flyinggorilla/whisper-foiling-catamaran/3dprinting/line-holder-2.jpg

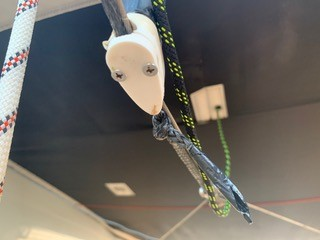
3dprinting/line-holder-2.jpg
