flyinggorilla/whisper-foiling-catamaran/3dprinting/original ride height adjustment wheel.jpg

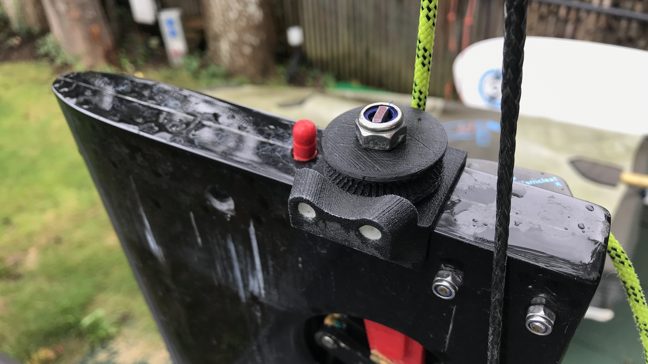
3dprinting/original ride height adjustment wheel.jpg
