flyinggorilla/whisper-foiling-catamaran/3dprinting/ride height knob small.jpg

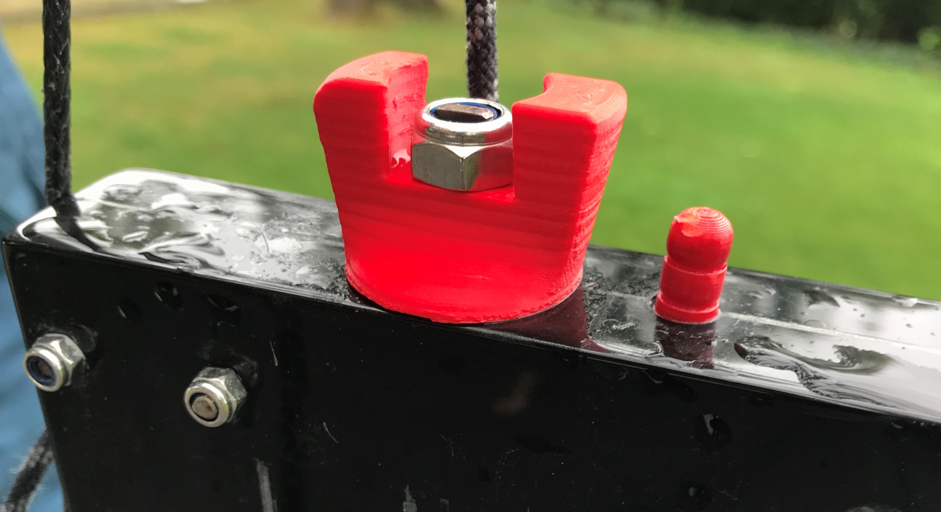
3dprinting/ride height knob small.jpg
