flyinggorilla/whisper-foiling-catamaran/3dprinting/ride height knob.jpg

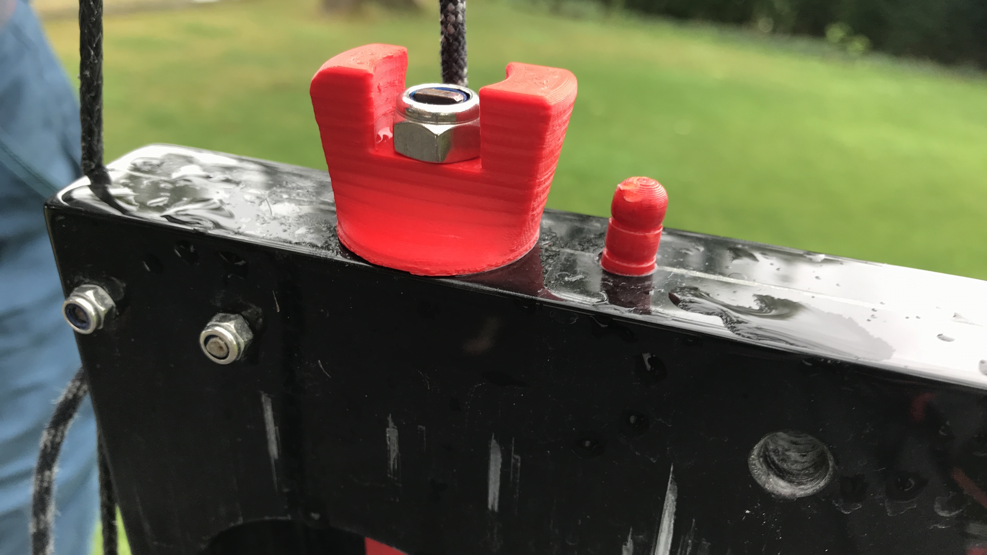
3dprinting/ride height knob.jpg
