flyinggorilla/whisper-foiling-catamaran/3dprinting/ride height knob.png

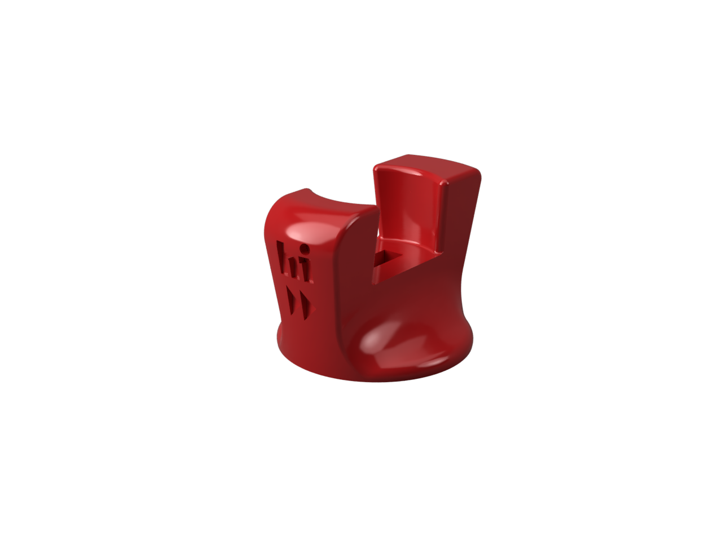
3dprinting/ride height knob.png
