flyinggorilla/whisper-foiling-catamaran/3dprinting/ride height system closeup 1.jpg

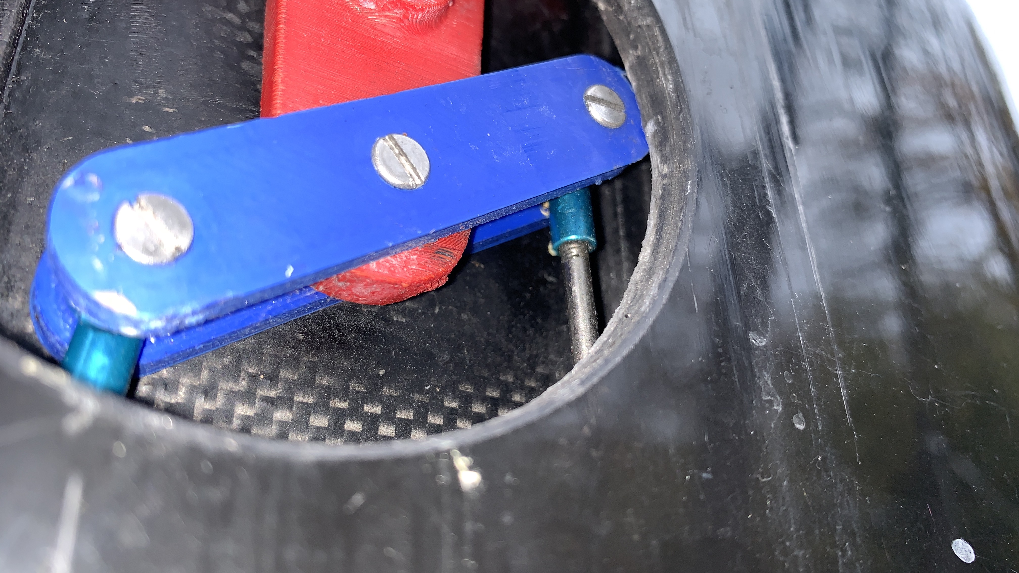
3dprinting/ride height system closeup 1.jpg
