flyinggorilla/whisper-foiling-catamaran/3dprinting/ride height system closeup 3.jpg

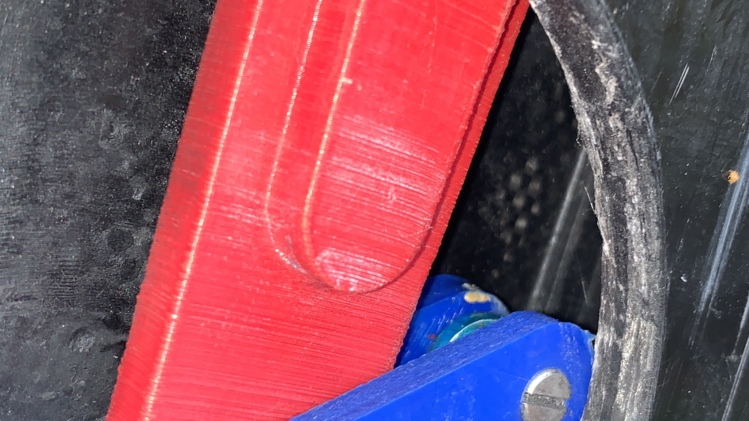
3dprinting/ride height system closeup 3.jpg
