flyinggorilla/whisper-foiling-catamaran/3dprinting/ride height system closeup 4.jpg

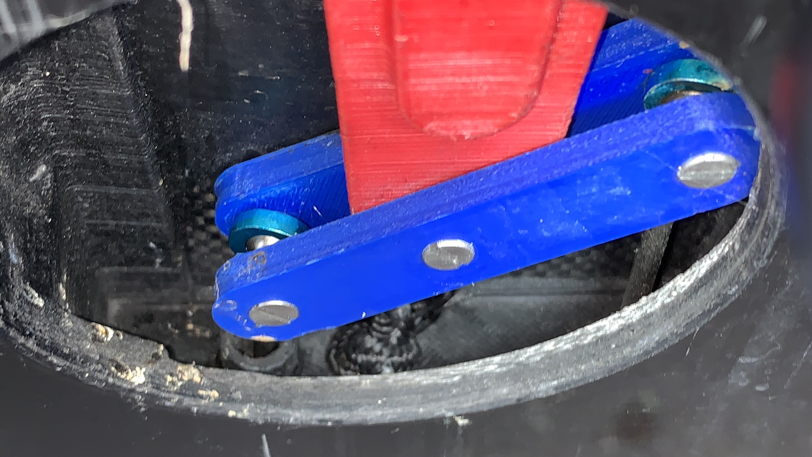
3dprinting/ride height system closeup 4.jpg
