flyinggorilla/whisper-foiling-catamaran/3dprinting/ride height system closeup 5.jpg

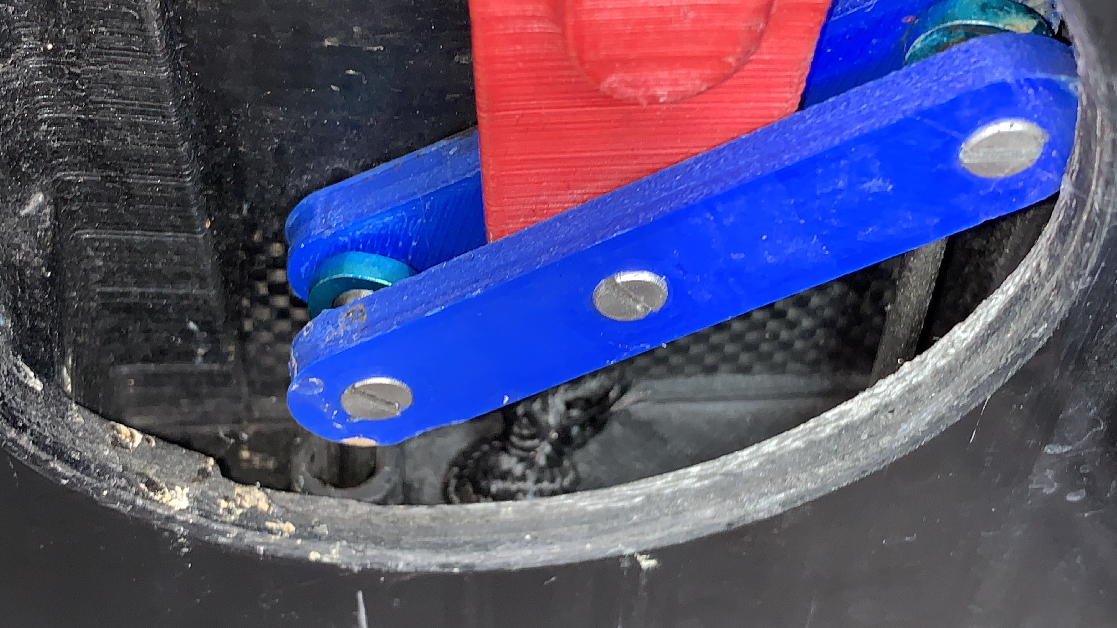
3dprinting/ride height system closeup 5.jpg
