flyinggorilla/whisper-foiling-catamaran/3dprinting/ride height system closeup 6.jpg

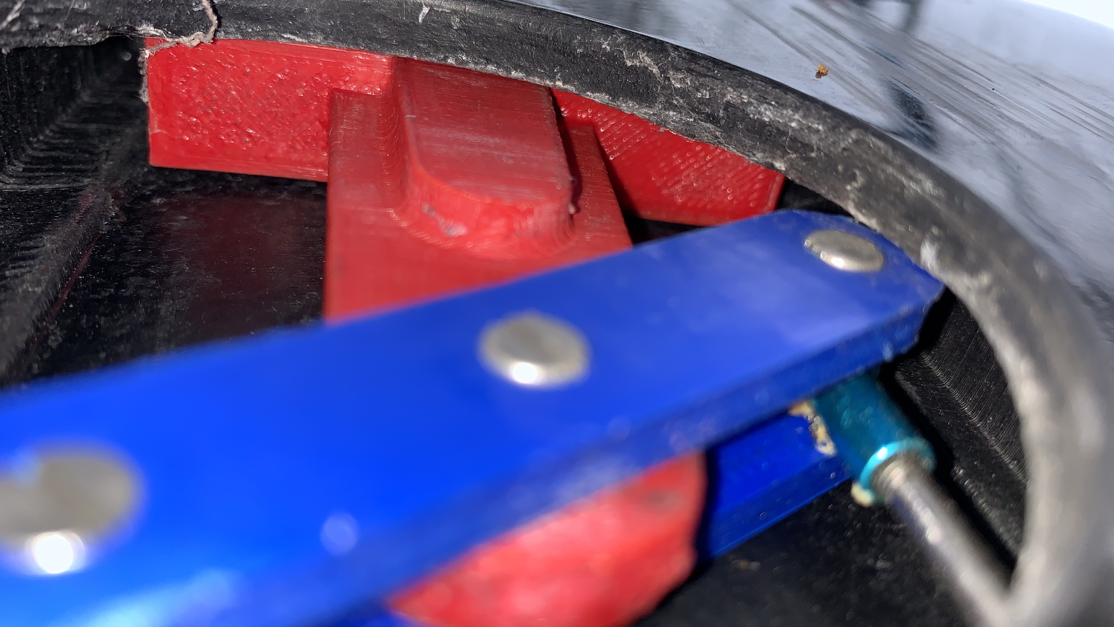
3dprinting/ride height system closeup 6.jpg
