flyinggorilla/whisper-foiling-catamaran/3dprinting/rudder holder insert and twist to lock.jpg

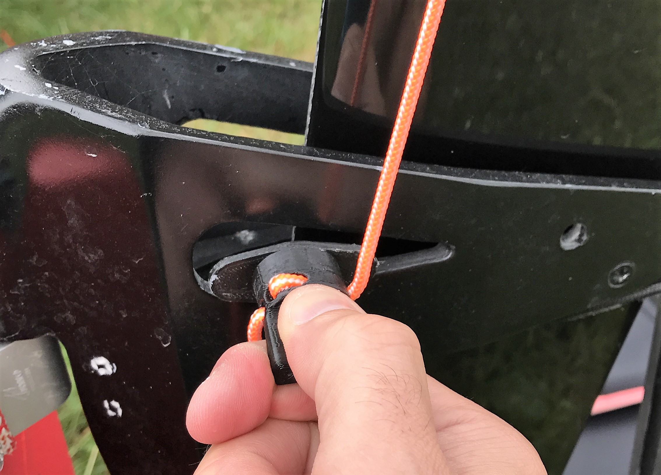
3dprinting/rudder holder insert and twist to lock.jpg
