flyinggorilla/whisper-foiling-catamaran/3dprinting/rudder holder v1 locked.jpg

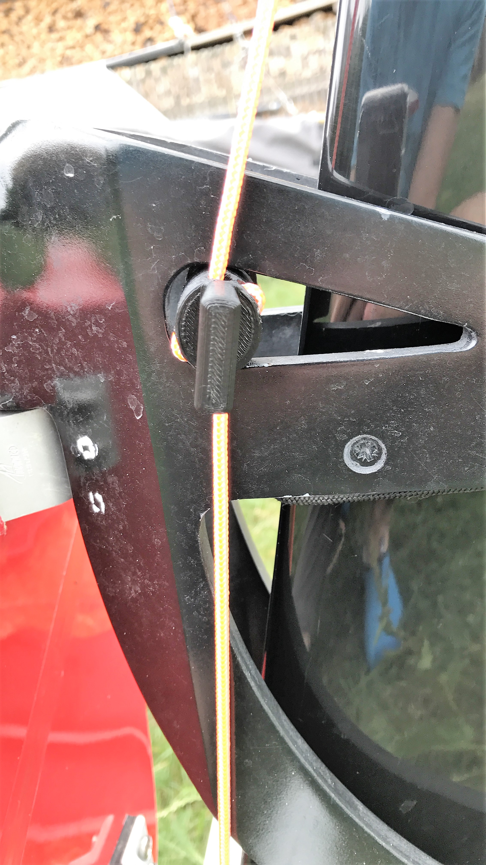
3dprinting/rudder holder v1 locked.jpg
