flyinggorilla/whisper-foiling-catamaran/3dprinting/rudder holder v1 twist to lock.jpg

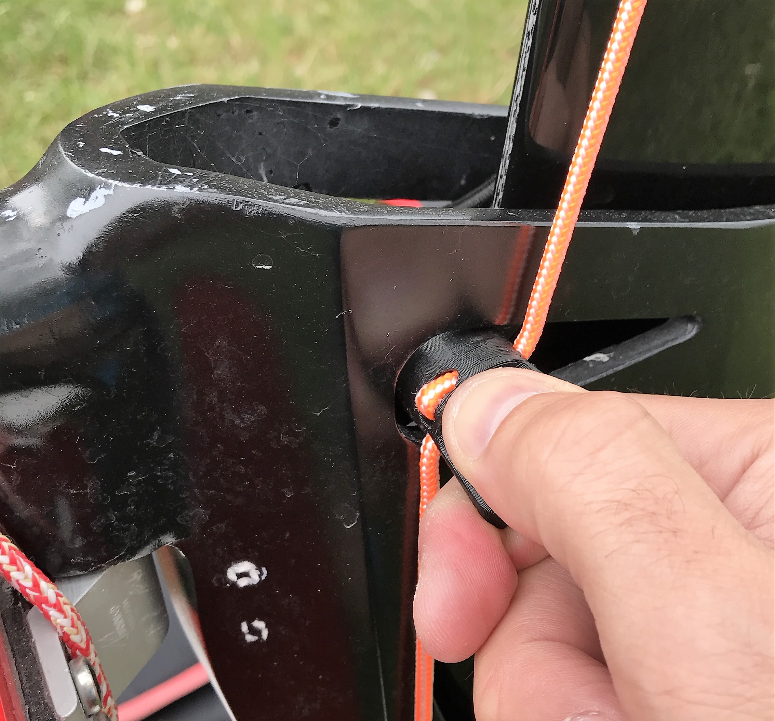
3dprinting/rudder holder v1 twist to lock.jpg
