flyinggorilla/whisper-foiling-catamaran/3dprinting/rudder holder v1.jpg

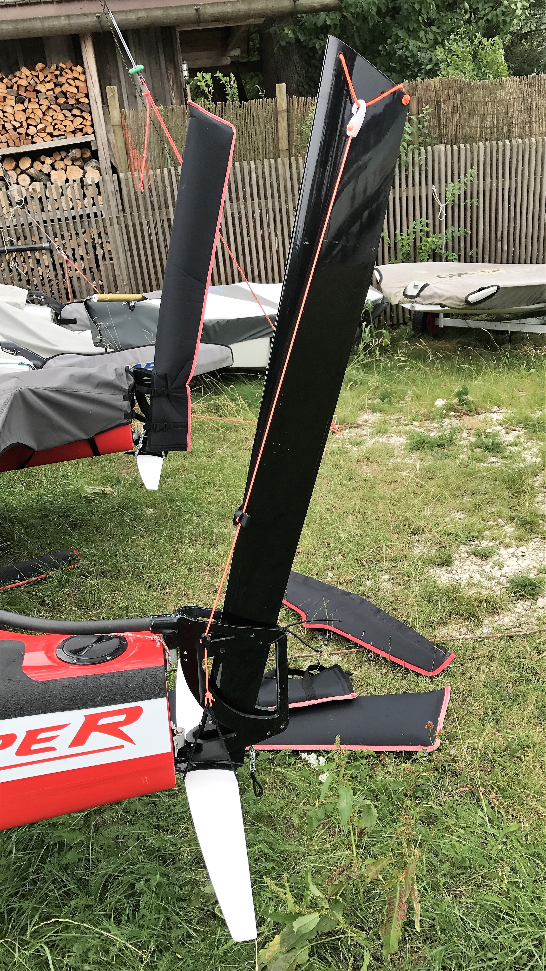
3dprinting/rudder holder v1.jpg
