flyinggorilla/whisper-foiling-catamaran/3dprinting/T part with and without helicoil 3.jpg

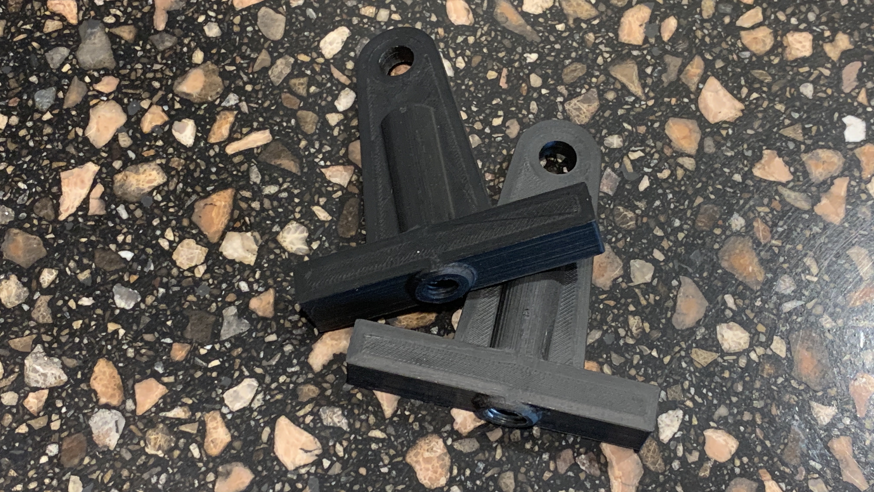
3dprinting/T part with and without helicoil 3.jpg
