flyinggorilla/whisper-foiling-catamaran/3dprinting/tools fit to tighten the nut.jpg

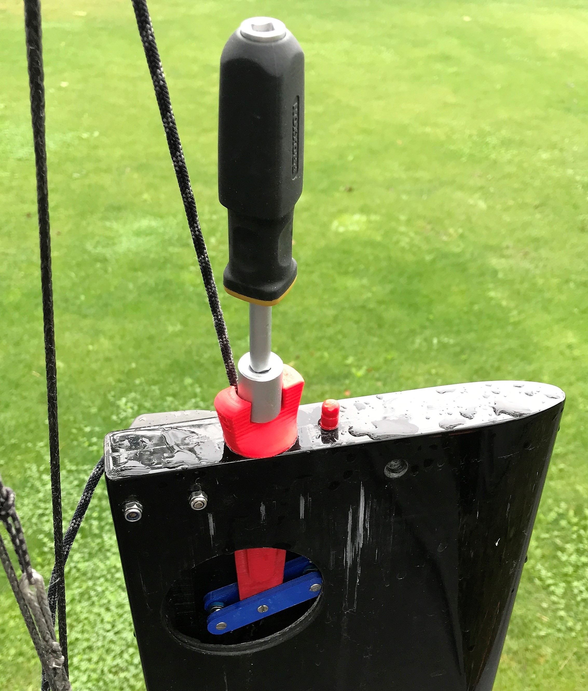
3dprinting/tools fit to tighten the nut.jpg
