flyinggorilla/whisper-foiling-catamaran/3dprinting/VelocitekSpeedpuckHolder for Whisper Catamaran v4.PNG

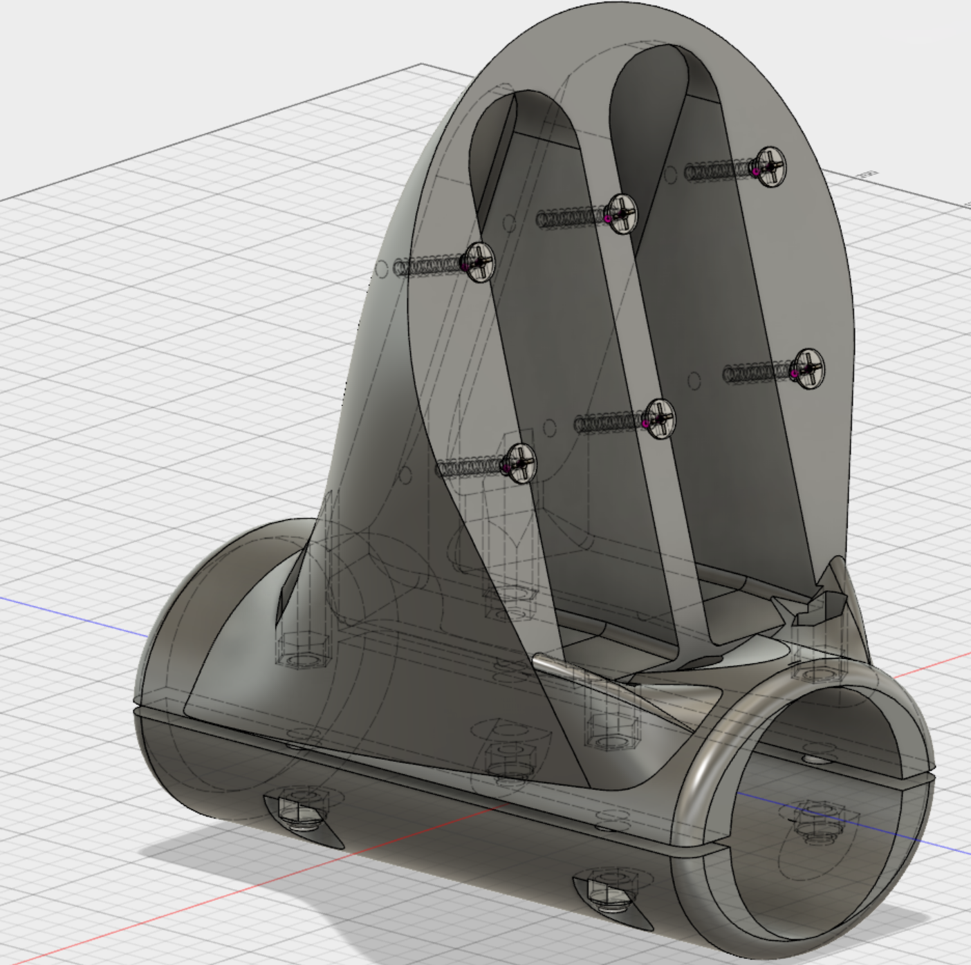
3dprinting/VelocitekSpeedpuckHolder for Whisper Catamaran v4.PNG
