flyinggorilla/whisper-foiling-catamaran/3dprinting/wand arm on rod.jpg

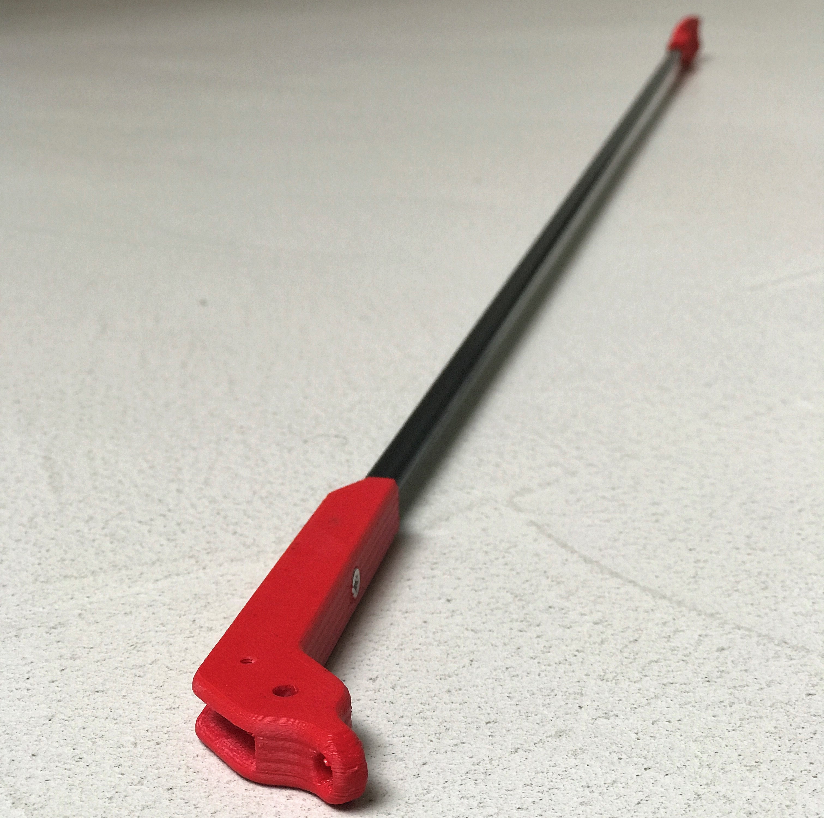
3dprinting/wand arm on rod.jpg
