flyinggorilla/whisper-foiling-catamaran/3dprinting/wand arm.jpg

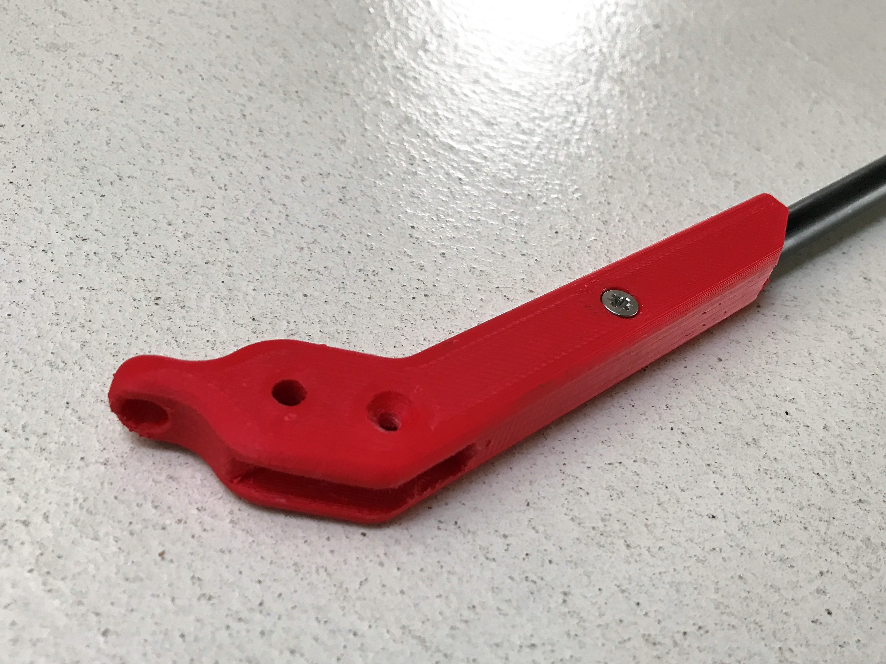
3dprinting/wand arm.jpg
