flyinggorilla/whisper-foiling-catamaran/3dprinting/wand diagonalpic.jpg

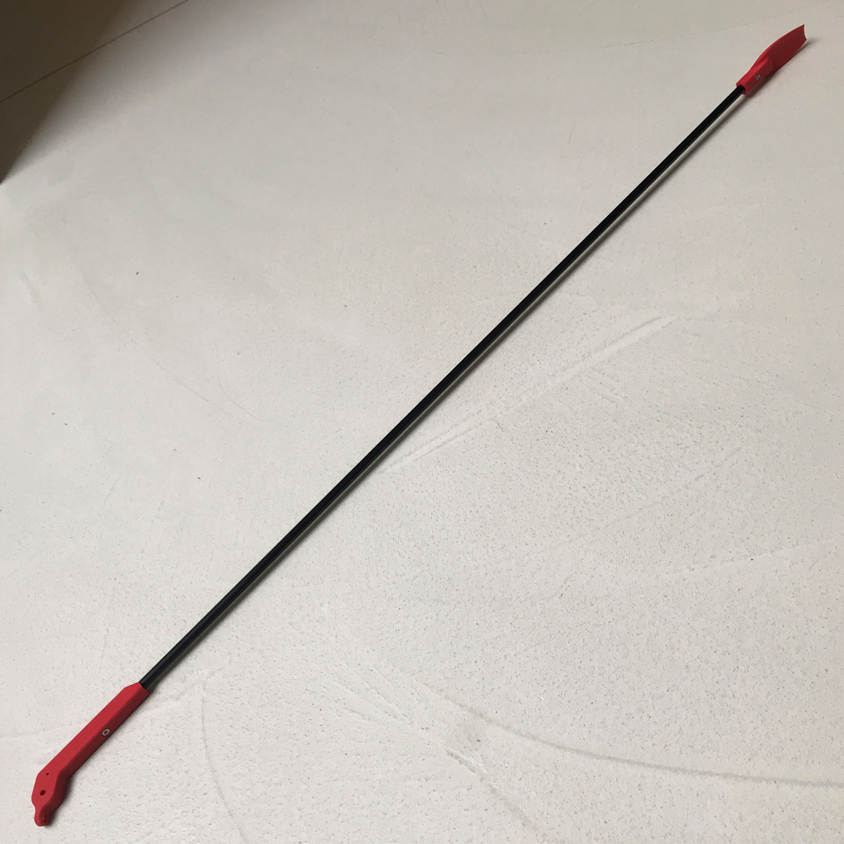
3dprinting/wand diagonalpic.jpg
