flyinggorilla/whisper-foiling-catamaran/3dprinting/wand paddel v1.jpg

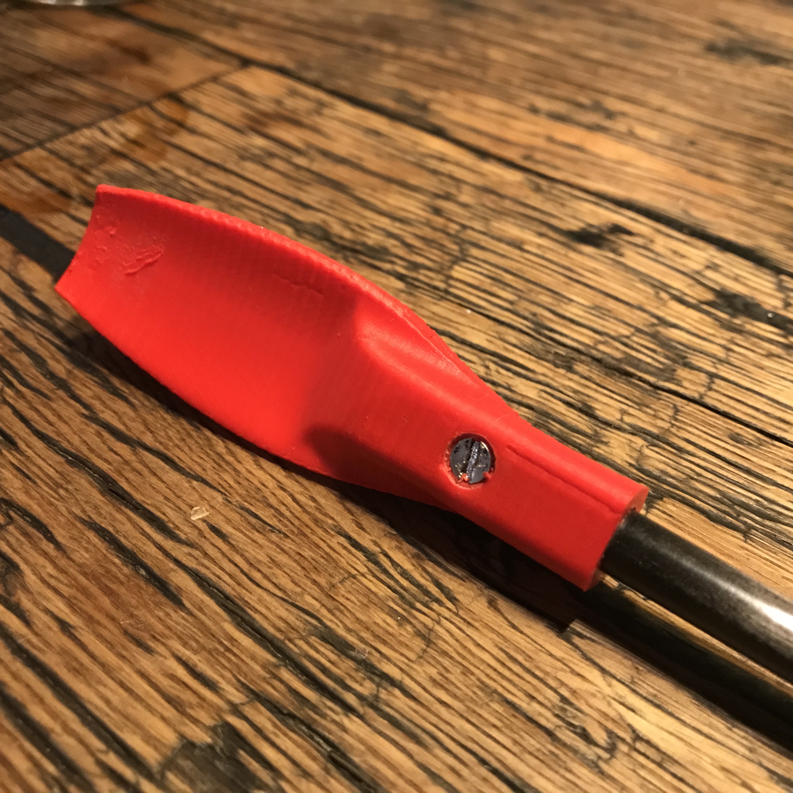
3dprinting/wand paddel v1.jpg
