flyinggorilla/whisper-foiling-catamaran/3dprinting/wand standing.jpg

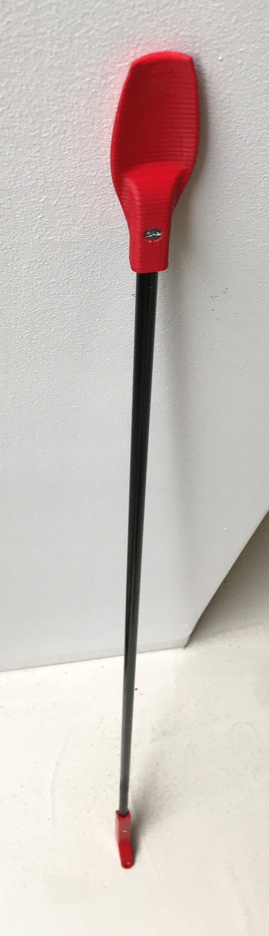
3dprinting/wand standing.jpg
