flyinggorilla/whisper-foiling-catamaran/3dprinting/wand_rect.jpg

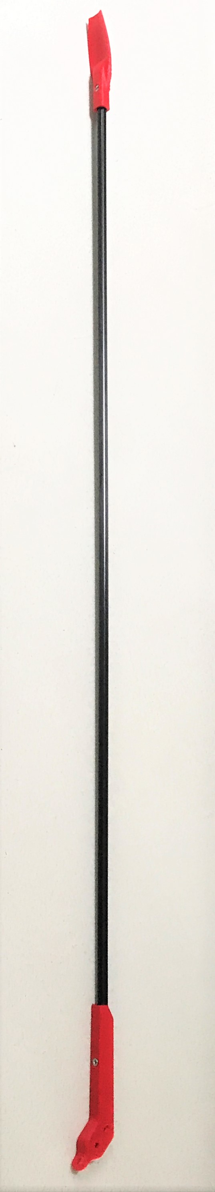
3dprinting/wand_rect.jpg
