flyinggorilla/whisper-foiling-catamaran/3dprinting/Whisper Ride Height T model A2.jpg

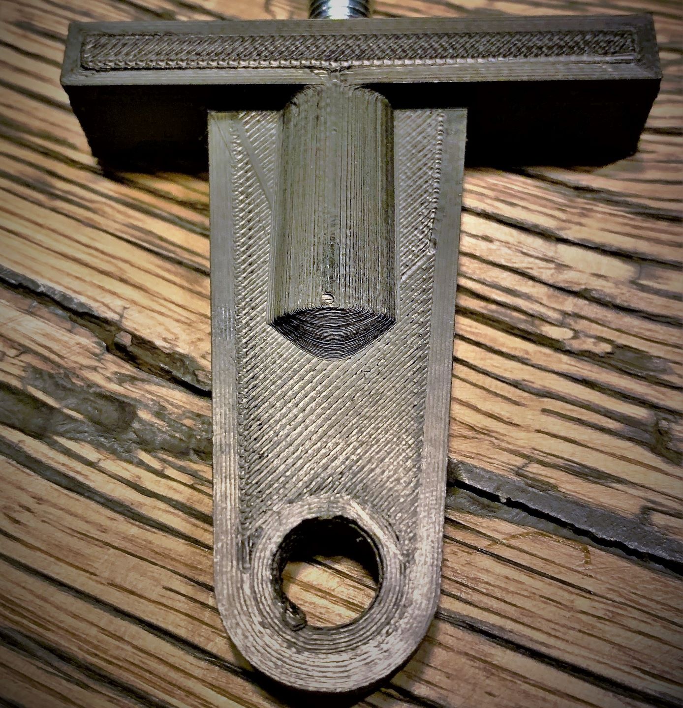
3dprinting/Whisper Ride Height T model A2.jpg
