flyinggorilla/whisper-foiling-catamaran/3dprinting/Whisper Ride Height T walls and infill.png

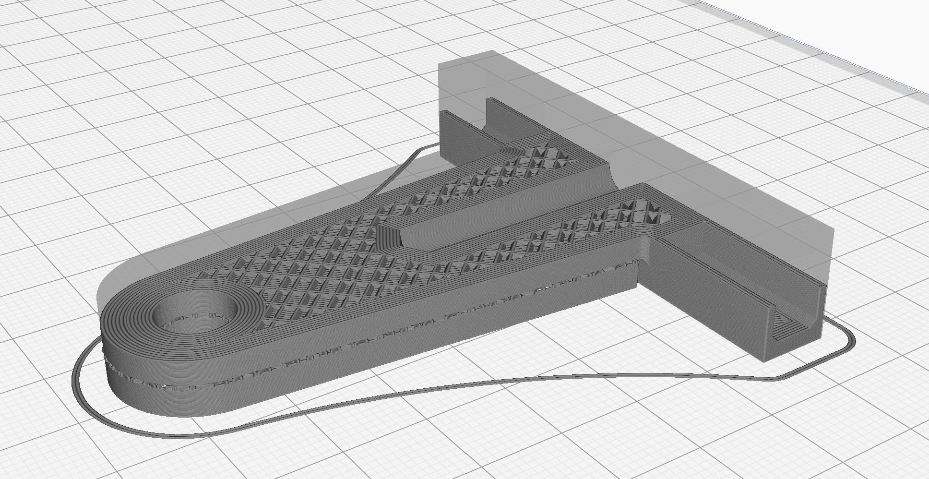
3dprinting/Whisper Ride Height T walls and infill.png
