flyinggorilla/whisper-foiling-catamaran/3dprinting/whisperfoiling.jpg

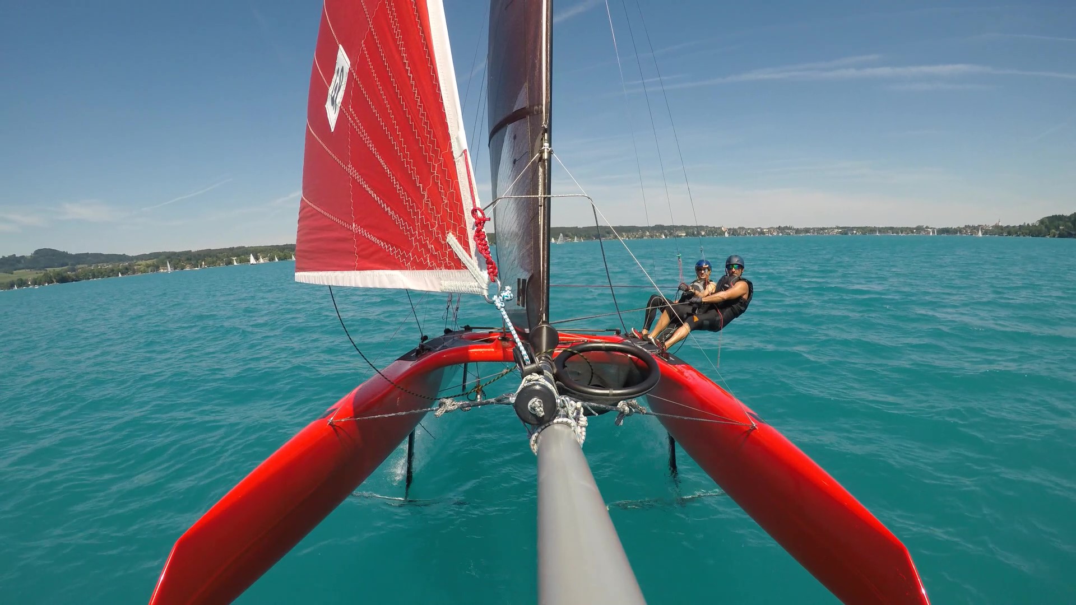
3dprinting/whisperfoiling.jpg
