flyinggorilla/whisper-foiling-catamaran/3dprinting/whisperrudderropetwister.png

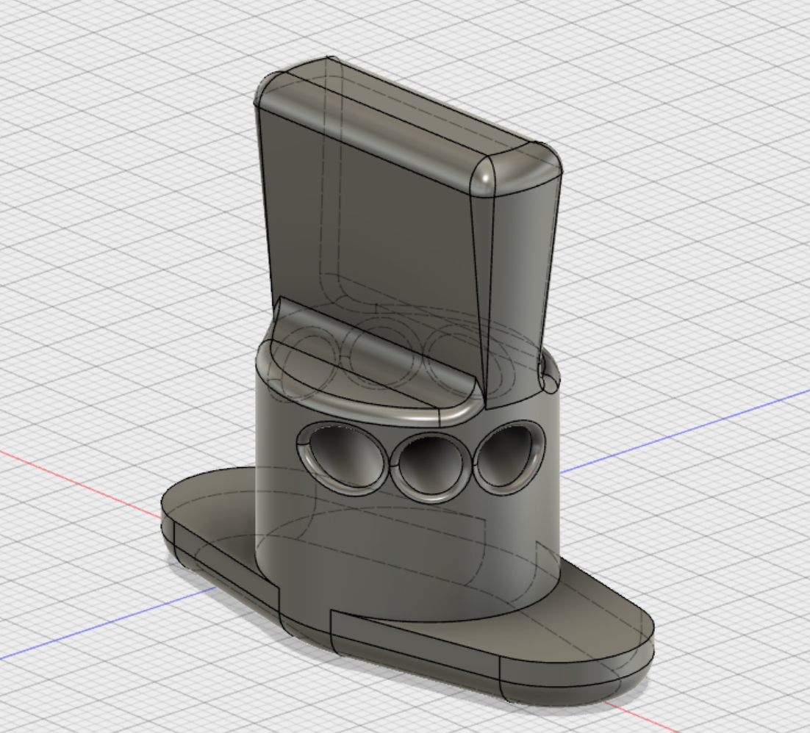
3dprinting/whisperrudderropetwister.png
