flyinggorilla/whisper-foiling-catamaran/slippingline.jpg

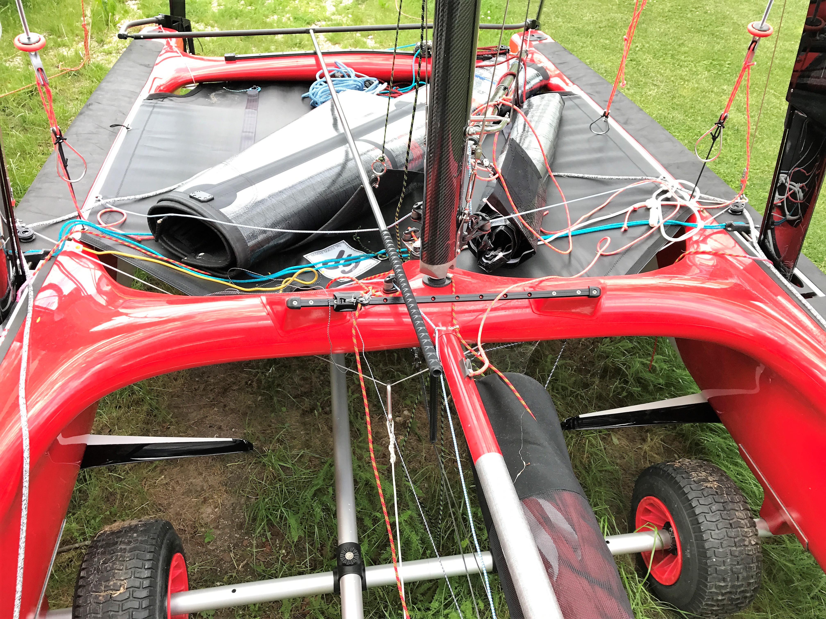
slippingline.jpg
