flyinggorilla/whisper-foiling-catamaran/untightruddermount.jpg

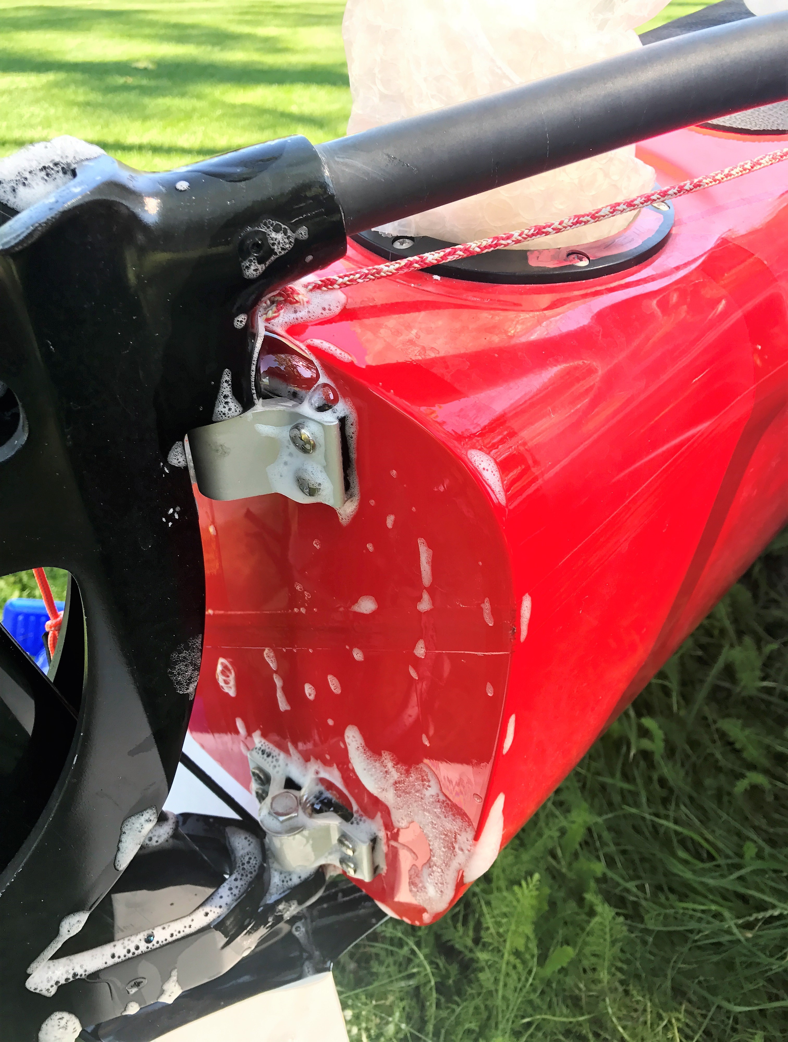
untightruddermount.jpg
