flyinggorilla/whisper-foiling-catamaran/3dprinting/ultimaker S5 printing T parts.jpg

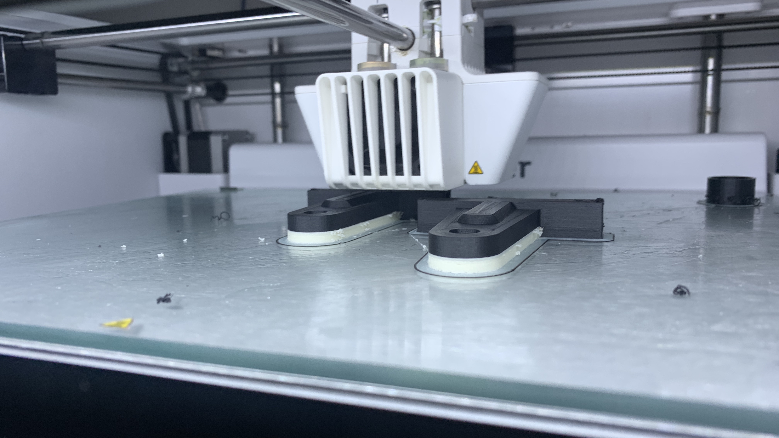
3dprinting/ultimaker S5 printing T parts.jpg
