flyinggorilla/whisper-foiling-catamaran/3dprinting/Whisper Ride Height T.stl

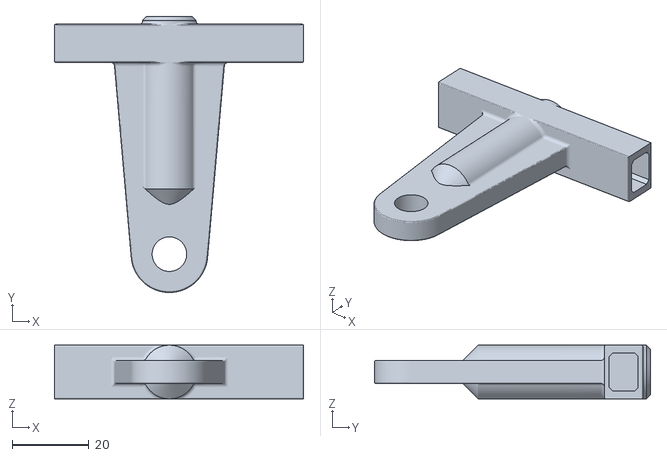
[picture p78: CAD file, 2020-08-04]
3dprinting/Whisper Ride Height T.stl
65.0 x 72.0 x 14.0
