flyinggorilla/whisper-foiling-catamaran/3dprinting/whisper-ride-height-T-with-threads.stl

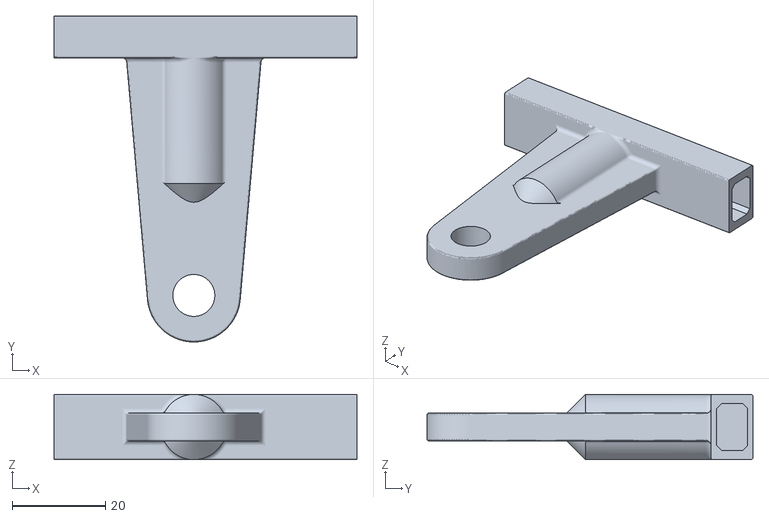
[picture p79: CAD file, 2020-08-04]
3dprinting/whisper-ride-height-T-with-threads.stl
65.0 x 70.0 x 14.0
