flyinggorilla/whisper-foiling-catamaran/3dprinting/assembled wand with carbon rod 1.jpg

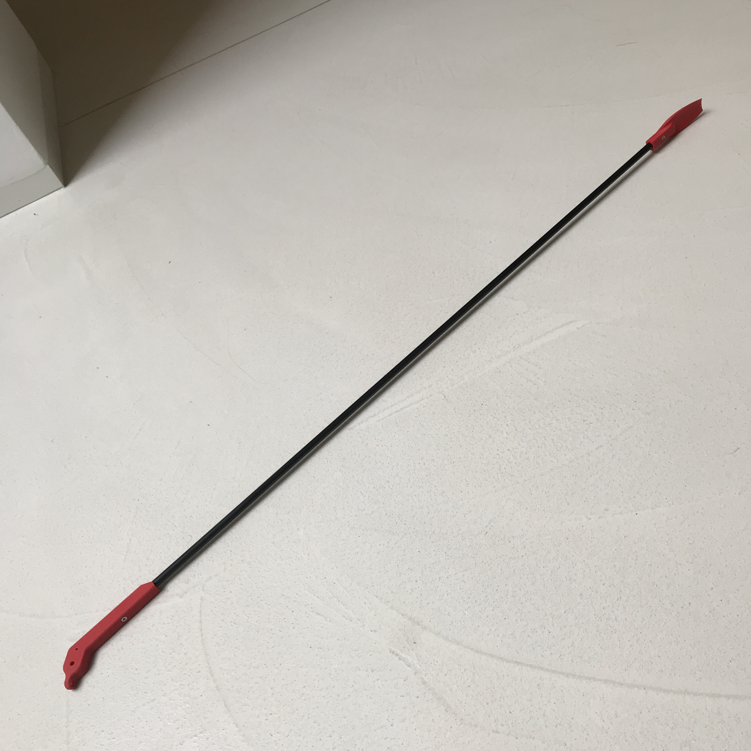
3dprinting/assembled wand with carbon rod 1.jpg
