flyinggorilla/whisper-foiling-catamaran/3dprinting/assembled wand with carbon rod 2.jpg

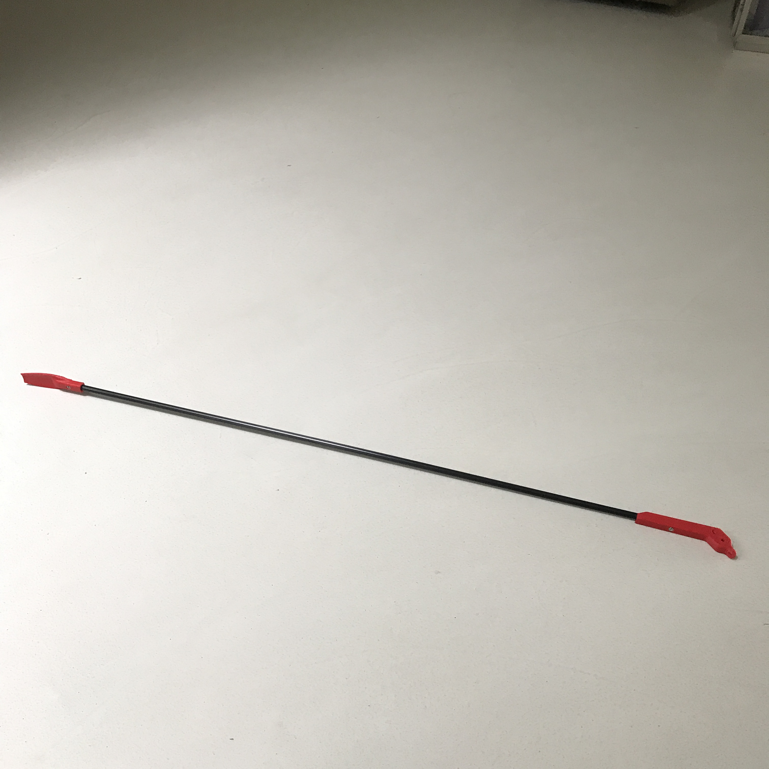
3dprinting/assembled wand with carbon rod 2.jpg
