flyinggorilla/whisper-foiling-catamaran/3dprinting/printing wand paddel 1.jpg

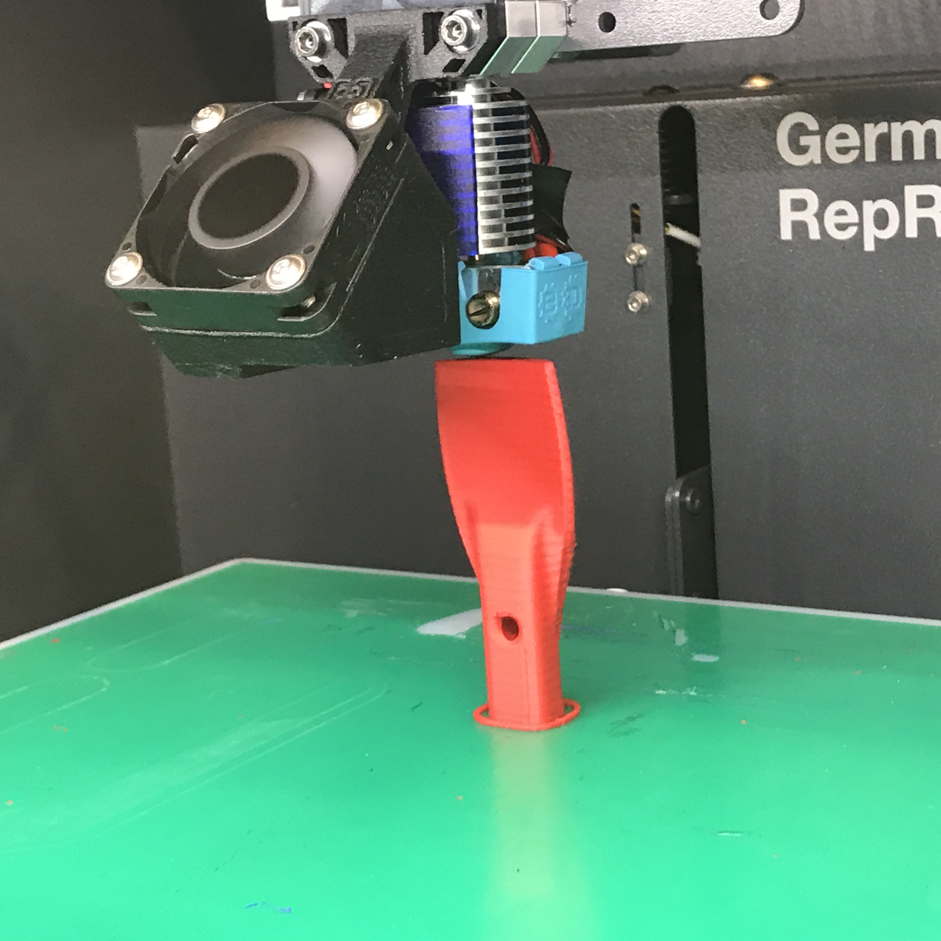
3dprinting/printing wand paddel 1.jpg
