flyinggorilla/whisper-foiling-catamaran/3dprinting/printing wand paddel 2.jpg

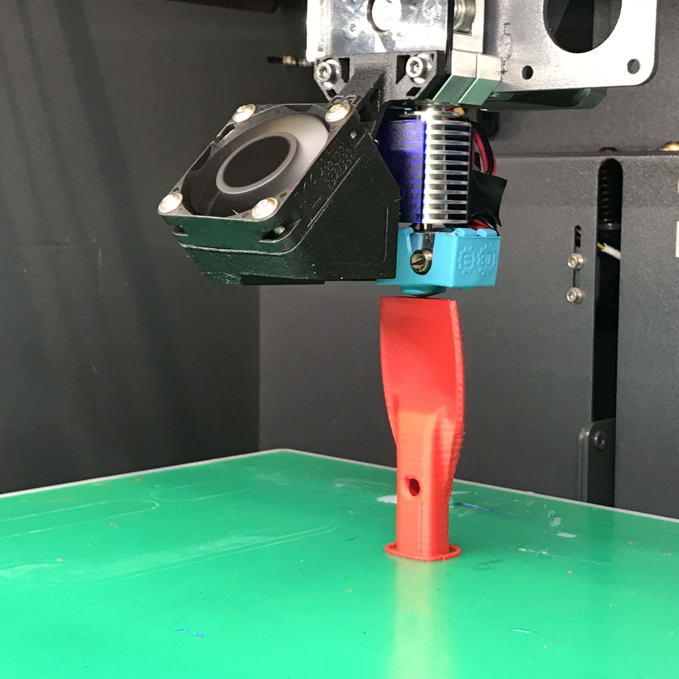
3dprinting/printing wand paddel 2.jpg
