flyinggorilla/whisper-foiling-catamaran/3dprinting/ride height system closeup T slide-guides closeup.jpg

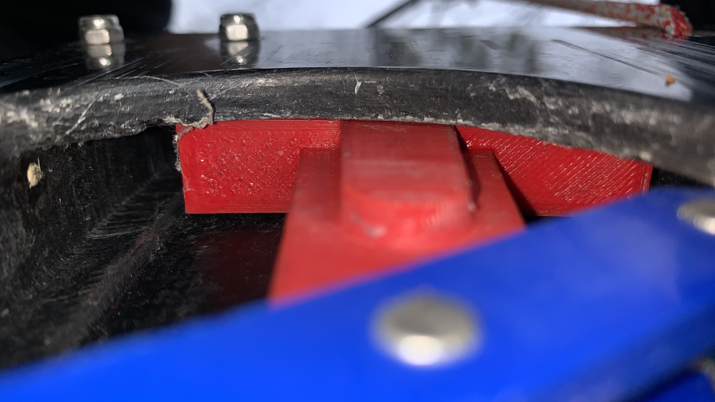
3dprinting/ride height system closeup T slide-guides closeup.jpg
