flyinggorilla/whisper-foiling-catamaran/3dprinting/T part printing closeup 2.jpg

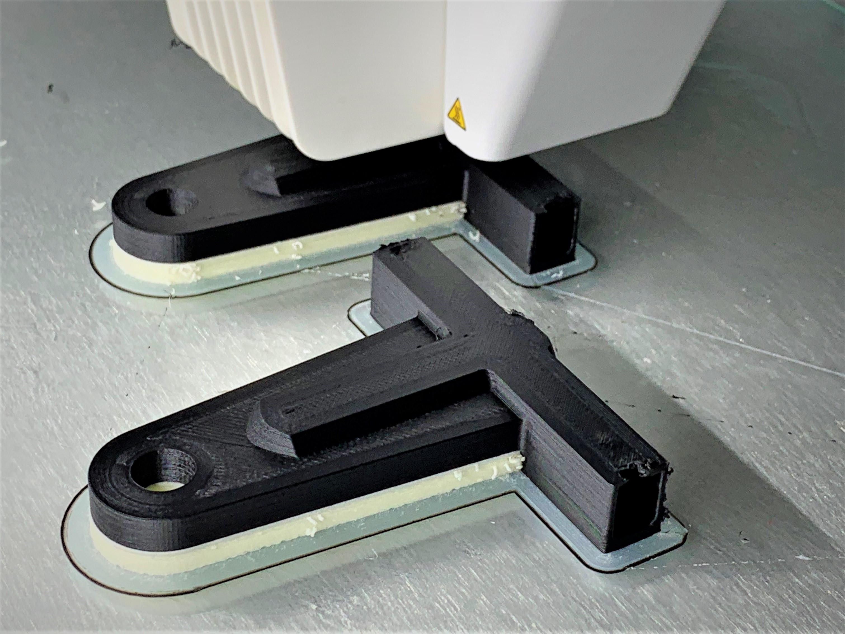
3dprinting/T part printing closeup 2.jpg
