flyinggorilla/whisper-foiling-catamaran/3dprinting/Whisper Ride Height T Print Horizontally for strength with soluble supports.png

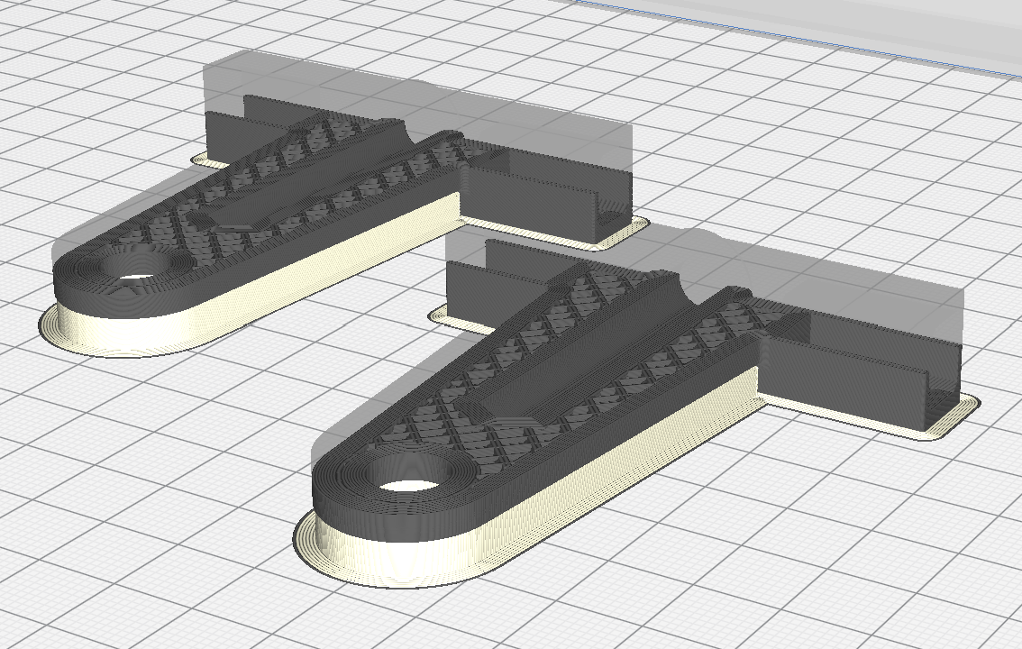
3dprinting/Whisper Ride Height T Print Horizontally for strength with soluble supports.png
