flyinggorilla/whisper-foiling-catamaran/3dprinting/T part with test screw.jpg

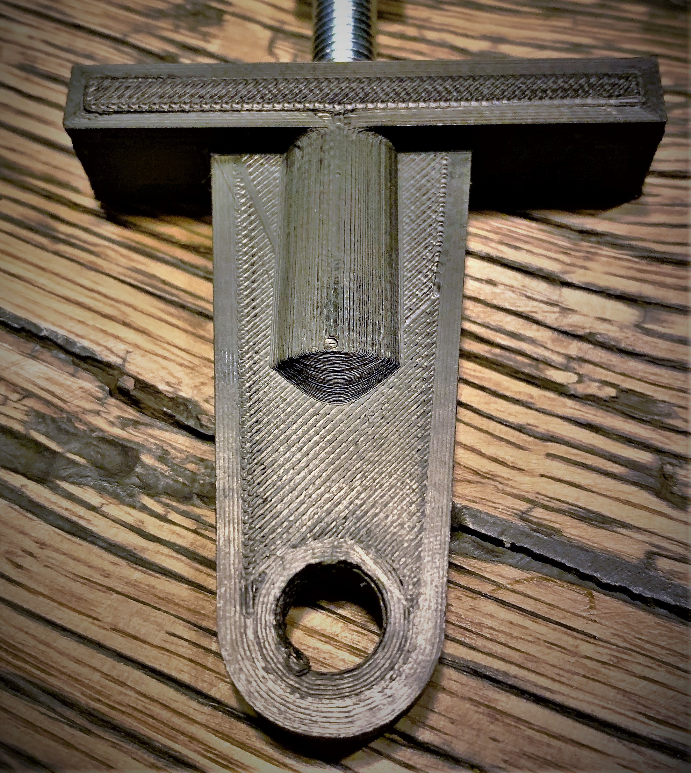
3dprinting/T part with test screw.jpg
